s-voelkl/BCN-2026SSTeamMagenta-Sensiq/sys-src/sensiq-aws/README.md

# Welcome to your CDK TypeScript project

This is a blank project for CDK development with TypeScript.

The `cdk.json` file tells the CDK Toolkit how to execute your app.

## Useful commands

* `yarn build`   compile typescript to js
* `yarn watch`   watch for changes and compile
* `yarn test`    perform the jest unit tests
* `yarn lint`    eslint and ruff linting
* `yarn lint:fix`   auto fix linting issues (if possible)
* `cdk deploy`  deploy this stack to your default AWS account/region
* `cdk diff`    compare deployed stack with current state
* `cdk synth`   emits the synthesized CloudFormation template
