s-voelkl/BCN-2026SSTeamMagenta-Sensiq/sys-src/sensiq-hardware/src/Test_WifiConnection.cpp

#include "WifiConnection.h"
#include "config.h"
#include <AUnit.h>

test(WifiConnection_connectToWiFi_connectsToWiFiAndReturnsTrue)
{
    // Act: Call the connectToWiFi function
    bool result = connectToWiFi();

    // Assert: Verify that the connection got established successfully
    assertTrue(result);
}
